alfo/artnet/PCB PDFs/ArtNet Node_etch_silk_bottom.pdf

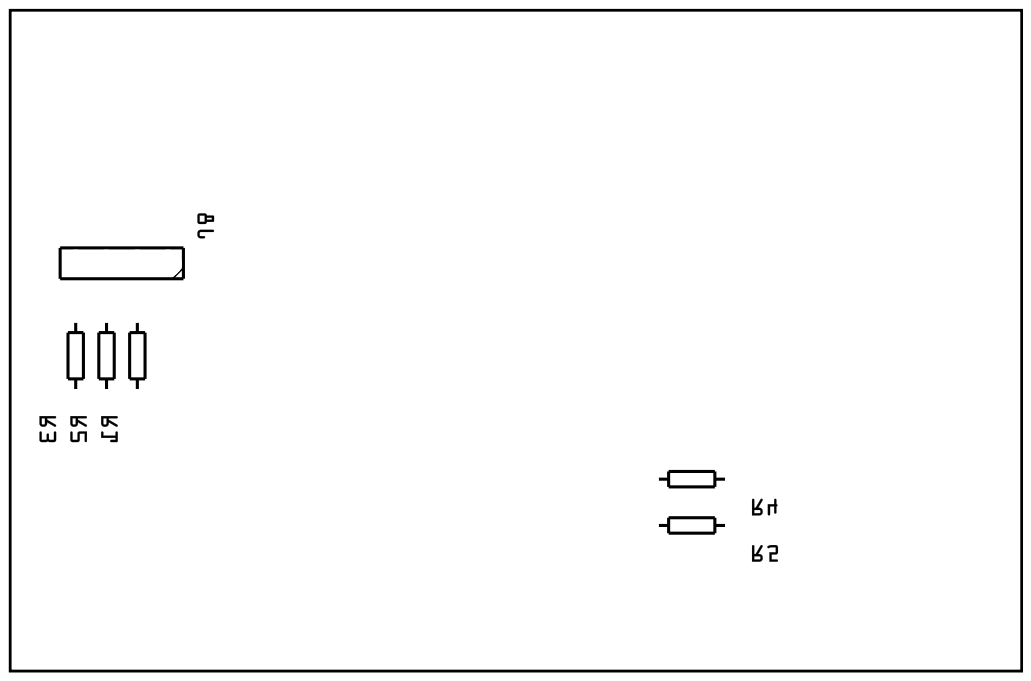
[picture p11: page 1]
