alfo/artnet/PCB PDFs/ArtNet Node_etch_silk_bottom_mirror.pdf

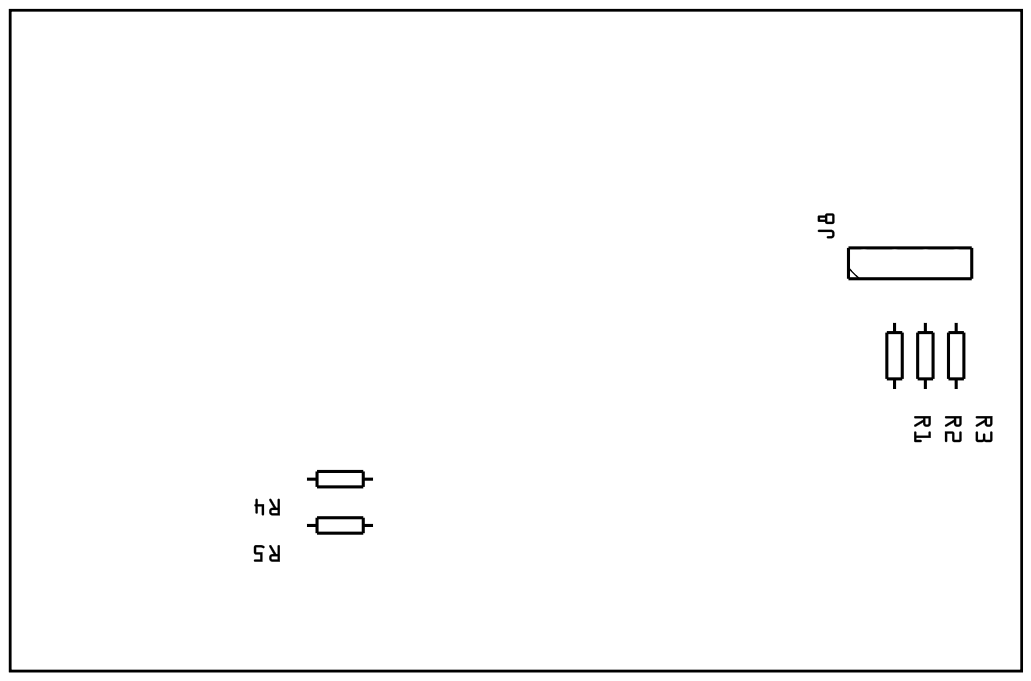
[picture p12: page 1]
