alfo/artnet/PCB PDFs/ArtNet Node_etch_silk_top.pdf

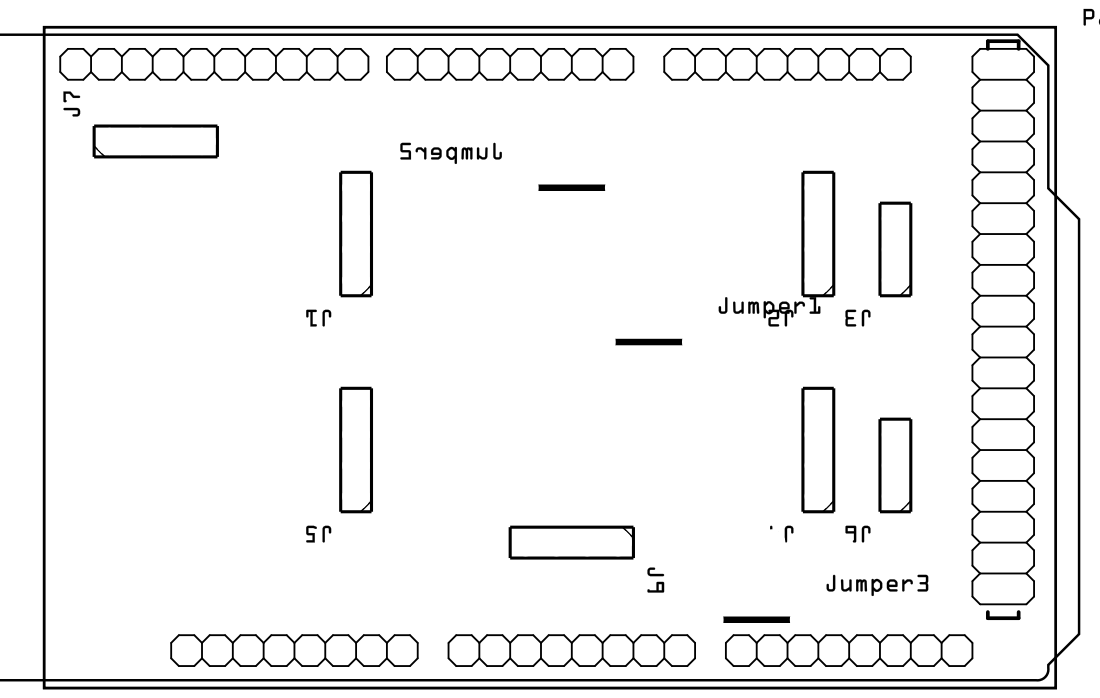
[picture p13: page 1]
