alfo/artnet/PCB PDFs/ArtNet Node_etch_silk_top_mirror.pdf

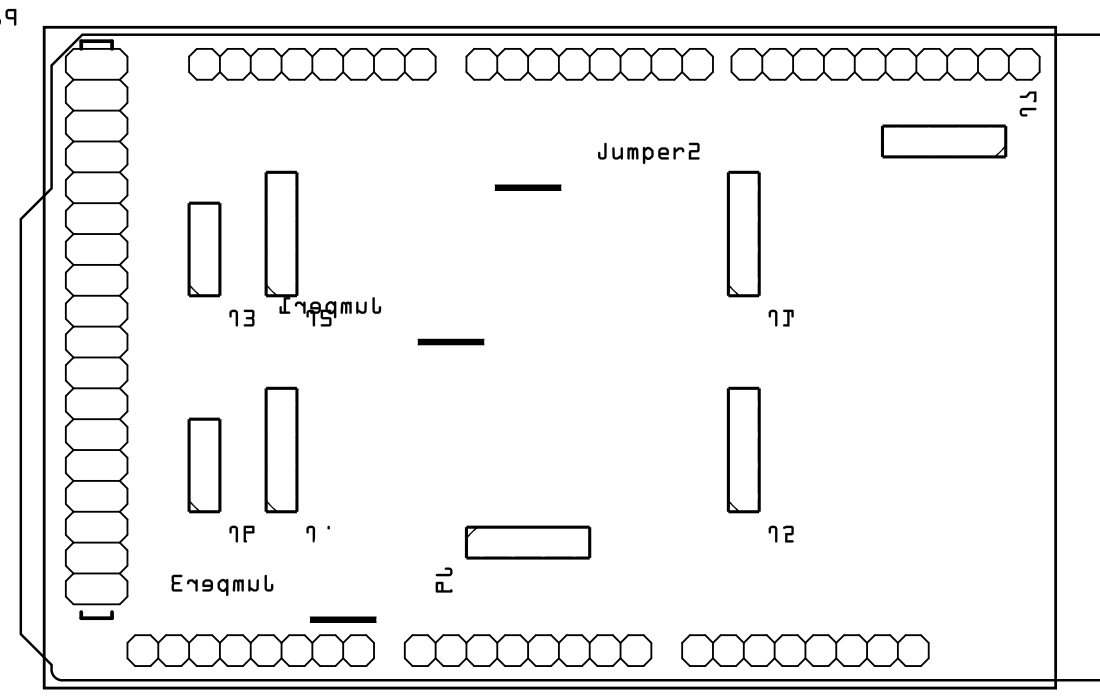
[picture p14: page 1]
